spapadim/ESPClock/util/ESPClockSetup/DroidMono16.h

/*
  Fontname: -FreeType-Droid Sans Mono-Medium-R-Normal--22-160-100-100-P-106-ISO10646-1
  Copyright: Digitized data copyright © 2007, Google Corporation.
  Capital A Height: 16, '1' Height: 16
  Calculated Max Values w=13 h=22 x= 6 y=13 dx=13 dy= 0 ascent=17 len=40
  Font Bounding box     w=17 h=29 x=-3 y=-6
  Calculated Min Values           x= 0 y=-5 dx= 0 dy= 0
  Pure Font   ascent =16 descent=-5
  X Font      ascent =16 descent=-5
  Max Font    ascent =17 descent=-5
*/
#include "u8g.h"
const u8g_fntpgm_uint8_t DroidMono16[3065] U8G_FONT_SECTION("DroidMono16") = {
  0,17,29,253,250,16,3,175,8,7,32,126,251,17,251,16,
  251,0,0,0,13,0,0,3,16,16,13,5,0,224,224,192,
  192,192,192,64,64,64,64,64,0,0,192,224,192,8,5,5,
  13,3,11,231,198,198,198,198,12,16,32,13,0,0,12,96,
  12,96,12,96,8,64,24,192,127,240,127,240,24,128,16,128,
  49,128,255,224,255,224,33,0,33,0,99,0,99,0,10,18,
  36,13,1,255,8,0,8,0,63,128,127,128,200,0,200,0,
  200,0,104,0,60,0,15,0,9,192,8,192,8,192,8,192,
  255,128,126,0,8,0,8,0,12,16,32,13,0,0,120,96,
  204,64,204,192,205,128,205,128,207,0,123,0,6,0,6,0,
  13,224,15,48,27,48,27,48,51,48,35,48,97,224,12,16,
  32,13,1,0,62,0,127,0,99,0,99,0,99,0,54,0,
  62,0,60,0,124,96,110,96,199,64,195,192,193,192,225,192,
  127,224,60,112,3,5,5,13,5,11,224,192,192,192,192,6,
  19,19,13,3,253,12,24,48,48,96,96,192,192,192,192,192,
  192,192,96,96,48,48,24,12,6,19,19,13,4,253,192,96,
  48,48,24,24,12,12,12,12,12,12,12,24,24,48,48,96,
  192,11,10,20,13,1,7,6,0,4,0,4,0,68,96,255,
  224,14,0,10,0,27,0,49,128,17,0,10,10,20,13,1,
  3,12,0,12,0,12,0,12,0,255,192,255,192,12,0,12,
  0,12,0,12,0,4,5,5,13,4,254,112,112,96,224,192,
  7,2,2,13,3,5,254,254,3,3,3,13,5,0,224,224,
  224,9,16,32,13,2,0,1,128,3,0,3,0,2,0,6,
  0,6,0,12,0,12,0,24,0,24,0,48,0,48,0,32,
  0,96,0,96,0,192,0,10,16,32,13,1,0,30,0,63,
  0,97,128,97,128,192,192,192,192,192,192,192,192,192,192,192,
  192,192,192,192,192,97,128,97,128,63,0,30,0,6,16,16,
  13,2,0,12,60,124,236,76,12,12,12,12,12,12,12,12,
  12,12,12,10,16,32,13,2,0,62,0,127,0,67,128,1,
  128,1,128,1,128,1,128,3,0,6,0,14,0,28,0,24,
  0,48,0,96,0,255,192,255,192,9,16,32,13,2,0,62,
  0,255,0,65,128,1,128,1,128,1,128,3,0,60,0,63,
  0,3,128,1,128,1,128,1,128,3,128,255,0,126,0,11,
  16,32,13,1,0,1,128,3,128,7,128,7,128,13,128,25,
  128,25,128,49,128,33,128,97,128,193,128,255,224,255,224,1,
  128,1,128,1,128,9,16,32,13,2,0,127,0,255,0,192,
  0,192,0,192,0,192,0,254,0,255,0,3,128,1,128,1,
  128,1,128,1,128,3,0,255,0,124,0,10,16,32,13,1,
  0,15,128,31,128,48,0,96,0,96,0,192,0,223,0,255,
  128,225,192,192,192,192,192,192,192,192,192,97,128,63,128,30,
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
