spapadim/ESPClock/util/ESPClockSetup/DroidMono18.h

/*
  Fontname: -FreeType-Droid Sans Mono-Medium-R-Normal--25-180-100-100-P-120-ISO10646-1
  Copyright: Digitized data copyright © 2007, Google Corporation.
  Capital A Height: 18, '1' Height: 18
  Calculated Max Values w=15 h=25 x= 7 y=15 dx=15 dy= 0 ascent=19 len=46
  Font Bounding box     w=20 h=34 x=-4 y=-7
  Calculated Min Values           x= 0 y=-6 dx= 0 dy= 0
  Pure Font   ascent =18 descent=-6
  X Font      ascent =18 descent=-6
  Max Font    ascent =19 descent=-6
*/
//#include "u8g.h"
//const u8g_fntpgm_uint8_t DroidMono18[3416] U8G_FONT_SECTION("DroidMono18") = {
static const uint8_t DroidMono18[3416] PROGMEM = {
  0,20,34,252,249,18,4,30,8,254,32,126,250,19,250,18,
  250,0,0,0,15,0,0,3,18,18,15,6,0,224,224,224,
  224,224,224,96,96,96,64,64,64,64,0,0,224,224,224,9,
  7,14,15,3,11,227,128,227,128,227,128,227,128,227,128,227,
  128,195,0,13,18,36,15,1,0,12,96,12,96,12,96,8,
  96,8,64,127,248,127,248,24,192,24,192,24,192,24,192,255,
  240,255,240,16,128,49,128,49,128,49,128,49,128,11,21,42,
  15,2,254,6,0,6,0,31,192,127,192,230,64,198,0,198,
  0,230,0,126,0,63,0,7,128,7,192,6,224,6,96,6,
  96,134,224,255,192,127,0,6,0,6,0,6,0,15,18,36,
  15,0,0,56,24,108,48,198,48,198,96,198,96,198,192,108,
  192,57,128,1,128,3,0,3,56,6,108,6,198,12,198,12,
  198,24,198,24,108,48,56,14,18,36,15,1,0,15,0,31,
  128,57,192,48,192,48,192,57,192,27,128,31,0,30,0,63,
  24,115,24,227,176,193,240,192,240,224,96,225,240,127,184,63,
  28,3,7,7,15,6,11,224,224,224,224,224,224,192,7,22,
  22,15,4,252,14,28,56,48,112,96,96,224,192,192,192,192,
  192,192,224,96,96,112,48,56,28,12,7,22,22,15,4,252,
  224,112,48,24,28,12,12,14,14,6,6,6,6,14,14,12,
  12,28,24,56,112,96,11,11,22,15,2,8,14,0,14,0,
  6,0,132,0,245,224,255,224,14,0,27,0,59,128,49,192,
  17,128,12,12,24,15,2,3,6,0,6,0,6,0,6,0,
  6,0,255,240,255,240,6,0,6,0,6,0,6,0,6,0,
  4,7,7,15,5,252,112,112,96,96,224,192,192,9,2,4,
  15,3,6,255,128,255,128,4,4,4,15,6,0,240,240,240,
  240,9,18,36,15,3,0,1,128,3,0,3,0,7,0,6,
  0,6,0,14,0,12,0,12,0,24,0,24,0,56,0,48,
  0,48,0,112,0,96,0,96,0,192,0,11,18,36,15,2,
  0,31,0,63,128,113,192,96,192,224,192,192,224,192,96,192,
  96,192,96,192,96,192,96,192,96,192,224,224,224,96,192,113,
  192,63,128,31,0,6,18,18,15,3,0,12,60,124,236,76,
  12,12,12,12,12,12,12,12,12,12,12,12,12,11,18,36,
  15,2,0,30,0,127,128,225,192,1,192,0,192,0,192,1,
  192,1,128,3,128,3,0,6,0,14,0,28,0,56,0,112,
  0,96,0,255,224,255,224,11,18,36,15,2,0,63,0,255,
  128,97,192,0,192,0,192,0,192,1,192,3,128,31,0,31,
  128,1,192,0,224,0,96,0,96,0,224,129,192,255,192,127,
  0,13,18,36,15,1,0,1,192,1,192,3,192,6,192,6,
  192,12,192,12,192,24,192,48,192,48,192,96,192,224,192,255,
  248,255,248,0,192,0,192,0,192,0,192,11,18,36,15,2,
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
