spapadim/ESPClock/util/ESPClockSetup/DroidSans16.h

/*
  Fontname: -FreeType-Droid Sans-Medium-R-Normal--22-160-100-100-P-111-ISO10646-1
  Copyright: Digitized data copyright © 2007, Google Corporation.
  Capital A Height: 16, '1' Height: 16
  Calculated Max Values w=19 h=22 x= 5 y=13 dx=20 dy= 0 ascent=17 len=54
  Font Bounding box     w=38 h=30 x=-12 y=-6
  Calculated Min Values           x=-2 y=-5 dx= 0 dy= 0
  Pure Font   ascent =16 descent=-5
  X Font      ascent =16 descent=-5
  Max Font    ascent =17 descent=-5
*/
#include "u8g.h"
const u8g_fntpgm_uint8_t DroidSans16[2887] U8G_FONT_SECTION("DroidSans16") = {
  0,38,30,244,250,16,3,167,7,227,32,126,251,17,251,16,
  251,0,0,0,6,0,0,3,16,16,6,2,0,224,224,224,
  224,224,224,192,192,192,64,64,0,0,224,224,224,6,6,6,
  8,1,10,204,204,204,204,204,204,14,16,32,14,0,0,4,
  48,4,48,12,32,12,32,127,252,8,96,8,96,24,64,24,
  64,24,64,255,248,16,192,16,192,48,128,48,128,48,128,10,
  18,36,12,1,255,8,0,8,0,63,128,127,128,200,0,200,
  0,200,0,104,0,60,0,15,0,9,192,8,192,8,192,9,
  192,255,128,126,0,8,0,8,0,16,16,32,18,1,0,120,
  24,120,16,204,48,204,32,204,96,204,64,204,222,205,158,121,
  179,123,51,2,51,6,51,4,51,12,51,8,30,24,30,14,
  16,32,15,1,0,30,0,63,0,97,128,97,128,97,128,51,
  0,62,0,28,0,126,24,103,24,195,176,193,240,192,224,224,
  240,127,184,63,28,2,6,6,4,1,10,192,192,192,192,192,
  192,5,19,19,7,1,253,24,48,48,96,96,224,192,192,192,
  192,192,192,192,192,96,96,48,48,24,5,19,19,7,1,253,
  192,96,96,48,48,56,24,24,24,24,24,24,24,24,48,48,
  96,96,192,10,10,20,12,1,7,12,0,12,0,12,0,204,
  192,255,192,12,0,30,0,51,0,51,0,49,0,10,10,20,
  12,1,3,12,0,12,0,12,0,12,0,255,192,255,192,12,
  0,12,0,12,0,12,0,3,5,5,6,1,254,96,96,192,
  192,192,5,2,2,7,1,5,248,248,3,3,3,6,1,0,
  224,224,224,8,16,16,8,0,0,3,2,6,6,12,12,8,
  24,24,48,48,32,96,96,192,192,10,16,32,12,1,0,30,
  0,63,0,97,128,97,128,192,192,192,192,192,192,192,192,192,
  192,192,192,192,192,192,192,97,128,97,128,63,0,30,0,6,
  16,16,12,2,0,12,60,124,236,76,12,12,12,12,12,12,
  12,12,12,12,12,10,16,32,12,1,0,62,0,255,0,67,
  128,1,128,1,128,1,128,1,128,3,0,6,0,14,0,28,
  0,24,0,48,0,96,0,255,192,255,192,10,16,32,12,1,
  0,62,0,255,0,67,128,1,128,1,128,1,128,3,0,60,
  0,63,0,1,128,0,192,0,192,0,192,1,192,255,128,126,
  0,11,16,32,12,0,0,1,128,3,128,7,128,5,128,13,
  128,25,128,17,128,49,128,97,128,65,128,255,224,255,224,1,
  128,1,128,1,128,1,128,10,16,32,12,1,0,127,128,255,
  128,192,0,192,0,192,0,192,0,254,0,255,128,1,128,0,
  192,0,192,0,192,0,192,1,128,255,128,126,0,10,16,32,
  12,1,0,15,128,63,128,48,0,96,0,96,0,192,0,223,
  0,255,128,225,192,192,192,192,192,192,192,64,192,97,128,63,
  128,30,0,10,16,32,12,1,0,255,192,255,192,0,192,1,
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
