spapadim/ESPClock/util/ESPClockSetup/DroidMono14.h

/*
  Fontname: -FreeType-Droid Sans Mono-Medium-R-Normal--19-140-100-100-P-90-ISO10646-1
  Copyright: Digitized data copyright © 2007, Google Corporation.
  Capital A Height: 14, '1' Height: 14
  Calculated Max Values w=11 h=20 x= 5 y=12 dx=11 dy= 0 ascent=15 len=36
  Font Bounding box     w=15 h=26 x=-3 y=-5
  Calculated Min Values           x= 0 y=-5 dx= 0 dy= 0
  Pure Font   ascent =14 descent=-5
  X Font      ascent =14 descent=-5
  Max Font    ascent =15 descent=-5
*/
#include "u8g.h"
const u8g_fntpgm_uint8_t DroidMono14[2452] U8G_FONT_SECTION("DroidMono14") = {
  0,15,26,253,251,14,3,62,6,223,32,126,251,15,251,14,
  251,0,0,0,11,0,0,3,14,14,11,4,0,192,192,192,
  192,192,192,64,64,64,64,0,64,224,192,6,5,5,11,2,
  9,204,204,204,204,204,11,14,28,11,0,0,8,64,24,192,
  24,192,16,128,127,224,16,128,49,128,49,128,33,0,255,192,
  33,0,33,0,99,0,66,0,9,16,32,11,1,255,8,0,
  8,0,63,0,107,0,200,0,200,0,232,0,124,0,15,0,
  9,128,9,128,9,128,239,0,254,0,8,0,8,0,11,14,
  28,11,0,0,113,128,217,0,137,0,139,0,218,0,118,0,
  4,0,4,0,13,192,11,96,26,32,18,32,19,96,49,192,
  10,14,28,11,1,0,60,0,102,0,102,0,102,0,102,0,
  60,0,56,0,121,128,205,128,199,128,199,0,195,0,111,128,
  120,192,2,5,5,11,4,9,192,192,192,192,192,5,17,17,
  11,3,253,24,48,96,96,64,192,192,192,192,192,192,192,64,
  96,96,48,24,5,17,17,11,3,253,192,96,48,48,16,24,
  24,24,24,24,24,24,16,48,48,96,192,9,9,18,11,1,
  6,8,0,8,0,8,0,235,128,255,128,28,0,54,0,54,
  0,34,0,9,9,18,11,1,2,8,0,8,0,8,0,8,
  0,255,128,8,0,8,0,8,0,8,0,3,5,5,11,4,
  253,96,96,192,192,192,5,2,2,11,3,4,248,248,3,3,
  3,11,4,0,224,224,224,7,14,14,11,2,0,6,4,12,
  12,8,24,24,48,48,32,96,96,64,192,9,14,28,11,1,
  0,62,0,119,0,99,0,193,128,193,128,193,128,193,128,193,
  128,193,128,193,128,193,128,99,0,119,0,62,0,5,14,14,
  11,2,0,24,56,216,152,24,24,24,24,24,24,24,24,24,
  24,9,14,28,11,1,0,62,0,243,0,65,128,1,128,1,
  128,1,128,3,0,6,0,12,0,24,0,48,0,96,0,192,
  0,255,128,9,14,28,11,1,0,62,0,243,0,1,128,1,
  128,1,128,3,0,60,0,7,0,1,128,1,128,1,128,1,
  128,231,0,126,0,10,14,28,11,1,0,3,0,7,0,15,
  0,11,0,27,0,51,0,35,0,99,0,195,0,255,192,3,
  0,3,0,3,0,3,0,9,14,28,11,1,0,255,0,192,
  0,192,0,192,0,192,0,254,0,71,0,1,128,1,128,1,
  128,1,128,1,128,199,0,252,0,9,14,28,11,1,0,15,
  0,57,0,96,0,64,0,192,0,222,0,243,0,193,128,193,
  128,193,128,193,128,97,128,119,0,30,0,9,14,28,11,1,
  0,255,128,1,128,1,0,3,0,3,0,2,0,6,0,4,
  0,12,0,12,0,24,0,24,0,16,0,48,0,9,14,28,
  11,1,0,62,0,99,0,193,128,193,128,193,128,103,0,60,
  0,126,0,195,0,193,128,193,128,193,128,103,0,62,0,9,
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
