spapadim/ESPClock/util/ESPClockSetup/DroidSans14.h

/*
  Fontname: -FreeType-Droid Sans-Medium-R-Normal--19-140-100-100-P-96-ISO10646-1
  Copyright: Digitized data copyright © 2007, Google Corporation.
  Capital A Height: 14, '1' Height: 14
  Calculated Max Values w=17 h=20 x= 4 y=12 dx=17 dy= 0 ascent=15 len=42
  Font Bounding box     w=31 h=26 x=-9 y=-5
  Calculated Min Values           x=-1 y=-5 dx= 0 dy= 0
  Pure Font   ascent =14 descent=-5
  X Font      ascent =14 descent=-5
  Max Font    ascent =15 descent=-5
*/
#include "u8g.h"
const u8g_fntpgm_uint8_t DroidSans14[2292] U8G_FONT_SECTION("DroidSans14") = {
  0,31,26,247,251,14,2,166,6,44,32,126,251,15,251,14,
  251,0,0,0,5,0,0,2,14,14,4,1,0,192,192,192,
  192,192,192,192,192,192,192,0,0,192,192,6,5,5,8,1,
  9,204,204,204,204,136,12,14,28,12,0,0,8,64,8,192,
  8,192,24,128,127,240,24,128,16,128,16,128,17,128,255,224,
  49,128,49,0,49,0,33,0,8,16,16,10,1,255,16,16,
  126,246,208,208,208,120,30,19,19,19,222,252,16,16,14,14,
  28,16,1,0,120,48,204,32,204,96,132,192,132,128,205,128,
  207,120,123,204,6,204,4,132,12,132,24,204,16,204,48,120,
  12,14,28,13,1,0,62,0,119,0,99,0,99,0,99,0,
  62,0,56,0,108,96,198,96,195,64,193,192,193,192,119,224,
  62,112,2,5,5,4,1,9,192,192,192,192,128,4,17,17,
  6,1,253,48,32,96,64,192,192,192,192,192,192,192,192,192,
  64,96,32,48,4,17,17,6,1,253,192,64,96,32,48,48,
  48,48,48,48,48,48,48,32,96,64,192,9,9,18,10,1,
  6,24,0,24,0,24,0,219,0,255,128,24,0,60,0,102,
  0,38,0,9,9,18,10,0,2,8,0,8,0,8,0,8,
  0,255,128,8,0,8,0,8,0,8,0,3,5,5,4,0,
  253,96,96,64,192,128,4,2,2,6,1,4,240,240,2,2,
  2,4,1,0,192,192,7,14,14,7,0,0,6,4,12,12,
  8,24,16,48,48,32,96,64,192,192,8,14,14,10,1,0,
  60,110,66,195,195,195,195,195,195,195,195,66,110,60,5,14,
  14,10,2,0,24,56,216,152,24,24,24,24,24,24,24,24,
  24,24,8,14,14,10,1,0,120,236,6,6,6,6,12,12,
  24,48,48,96,255,255,8,14,14,10,1,0,124,230,3,3,
  3,6,56,14,3,3,3,3,206,252,10,14,28,10,0,0,
  3,0,7,0,15,0,11,0,27,0,51,0,35,0,99,0,
  67,0,255,192,255,192,3,0,3,0,3,0,8,14,14,10,
  1,0,254,254,192,192,192,252,78,3,3,3,3,3,206,252,
  8,14,14,10,1,0,30,58,96,64,192,220,230,195,195,195,
  195,67,118,60,8,14,14,10,1,0,255,255,3,2,6,6,
  12,12,8,24,24,16,48,48,8,14,14,10,1,0,60,102,
  195,195,195,102,60,126,199,195,195,195,102,60,8,14,14,10,
  1,0,60,110,194,195,195,195,195,103,59,3,2,6,12,120,
  2,10,10,4,1,0,192,192,0,0,0,0,0,0,192,192,
  3,13,13,4,0,253,96,96,0,0,0,0,0,0,96,96,
  64,192,128,8,9,9,10,1,2,1,7,28,112,192,112,28,
  7,1,8,5,5,10,1,4,255,0,0,0,255,8,9,9,
  10,1,2,128,224,56,14,3,14,56,224,128,7,14,14,8,
  0,0,120,236,6,6,6,6,12,24,48,48,0,0,48,48,
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
