spapadim/ESPClock/util/ESPClockSetup/DroidSans50.h

/*
  Fontname: -FreeType-Droid Sans-Medium-R-Normal--69-500-100-100-P-332-ISO10646-1
  Copyright: Digitized data copyright © 2007, Google Corporation.
  Capital A Height: 0, '1' Height: 49
  Calculated Max Values w=36 h=51 x= 6 y= 0 dx=38 dy= 0 ascent=50 len=245
  Font Bounding box     w=118 h=90 x=-37 y=-18
  Calculated Min Values           x= 0 y=-1 dx= 0 dy= 0
  Pure Font   ascent =49 descent= 0
  X Font      ascent =49 descent= 0
  Max Font    ascent =50 descent=-1
*/
#include "u8g.h"
const u8g_fntpgm_uint8_t DroidSans50[2165] U8G_FONT_SECTION("DroidSans50") = {
  0,118,90,219,238,49,0,0,0,0,48,58,0,50,255,49,
  0,32,51,204,38,3,255,0,15,240,0,0,127,254,0,1,
  255,255,0,3,255,255,128,7,255,255,192,15,252,63,224,15,
  224,15,240,31,192,3,240,31,128,3,248,63,128,1,248,63,
  0,0,252,63,0,0,252,127,0,0,252,126,0,0,126,126,
  0,0,126,126,0,0,126,126,0,0,126,254,0,0,126,254,
  0,0,127,252,0,0,63,252,0,0,63,252,0,0,63,252,
  0,0,63,252,0,0,63,252,0,0,63,252,0,0,63,252,
  0,0,63,252,0,0,63,252,0,0,63,252,0,0,63,252,
  0,0,63,252,0,0,63,254,0,0,127,126,0,0,127,126,
  0,0,126,126,0,0,126,126,0,0,126,126,0,0,126,127,
  0,0,254,63,0,0,252,63,0,0,252,31,128,1,252,31,
  128,3,248,31,192,3,248,15,224,15,240,7,252,63,240,3,
  255,255,224,3,255,255,192,0,255,255,128,0,127,254,0,0,
  15,240,0,18,49,147,38,6,0,0,15,192,0,31,192,0,
  63,192,0,255,192,1,255,192,3,255,192,15,255,192,31,239,
  192,63,207,192,127,143,192,255,15,192,124,15,192,56,15,192,
  16,15,192,0,15,192,0,15,192,0,15,192,0,15,192,0,
  15,192,0,15,192,0,15,192,0,15,192,0,15,192,0,15,
  192,0,15,192,0,15,192,0,15,192,0,15,192,0,15,192,
  0,15,192,0,15,192,0,15,192,0,15,192,0,15,192,0,
  15,192,0,15,192,0,15,192,0,15,192,0,15,192,0,15,
  192,0,15,192,0,15,192,0,15,192,0,15,192,0,15,192,
  0,15,192,0,15,192,0,15,192,0,15,192,31,50,200,38,
  3,0,0,31,224,0,0,255,252,0,3,255,255,0,15,255,
  255,128,31,255,255,192,127,240,127,224,63,128,15,224,62,0,
  7,240,28,0,7,240,8,0,3,248,0,0,3,248,0,0,
  1,248,0,0,1,248,0,0,1,248,0,0,1,248,0,0,
  1,248,0,0,3,248,0,0,3,240,0,0,3,240,0,0,
  7,240,0,0,7,224,0,0,15,224,0,0,15,192,0,0,
  31,192,0,0,63,128,0,0,63,0,0,0,127,0,0,0,
  254,0,0,1,252,0,0,3,248,0,0,7,240,0,0,15,
  224,0,0,31,224,0,0,63,192,0,0,127,128,0,0,127,
  0,0,0,254,0,0,1,252,0,0,3,248,0,0,7,240,
  0,0,15,224,0,0,31,192,0,0,63,128,0,0,127,0,
  0,0,255,255,255,254,255,255,255,254,255,255,255,254,255,255,
  255,254,255,255,255,254,255,255,255,254,31,51,204,38,3,255,
  0,63,224,0,3,255,252,0,15,255,255,0,63,255,255,128,
  127,255,255,192,255,224,127,224,127,0,31,240,60,0,7,240,
  48,0,3,240,0,0,3,248,0,0,3,248,0,0,1,248,
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
